btb/PortableIIMemBoard/System Memory Board.kicad_sch

## KiCad design System Memory Board.kicad_sch (2024-03-25)

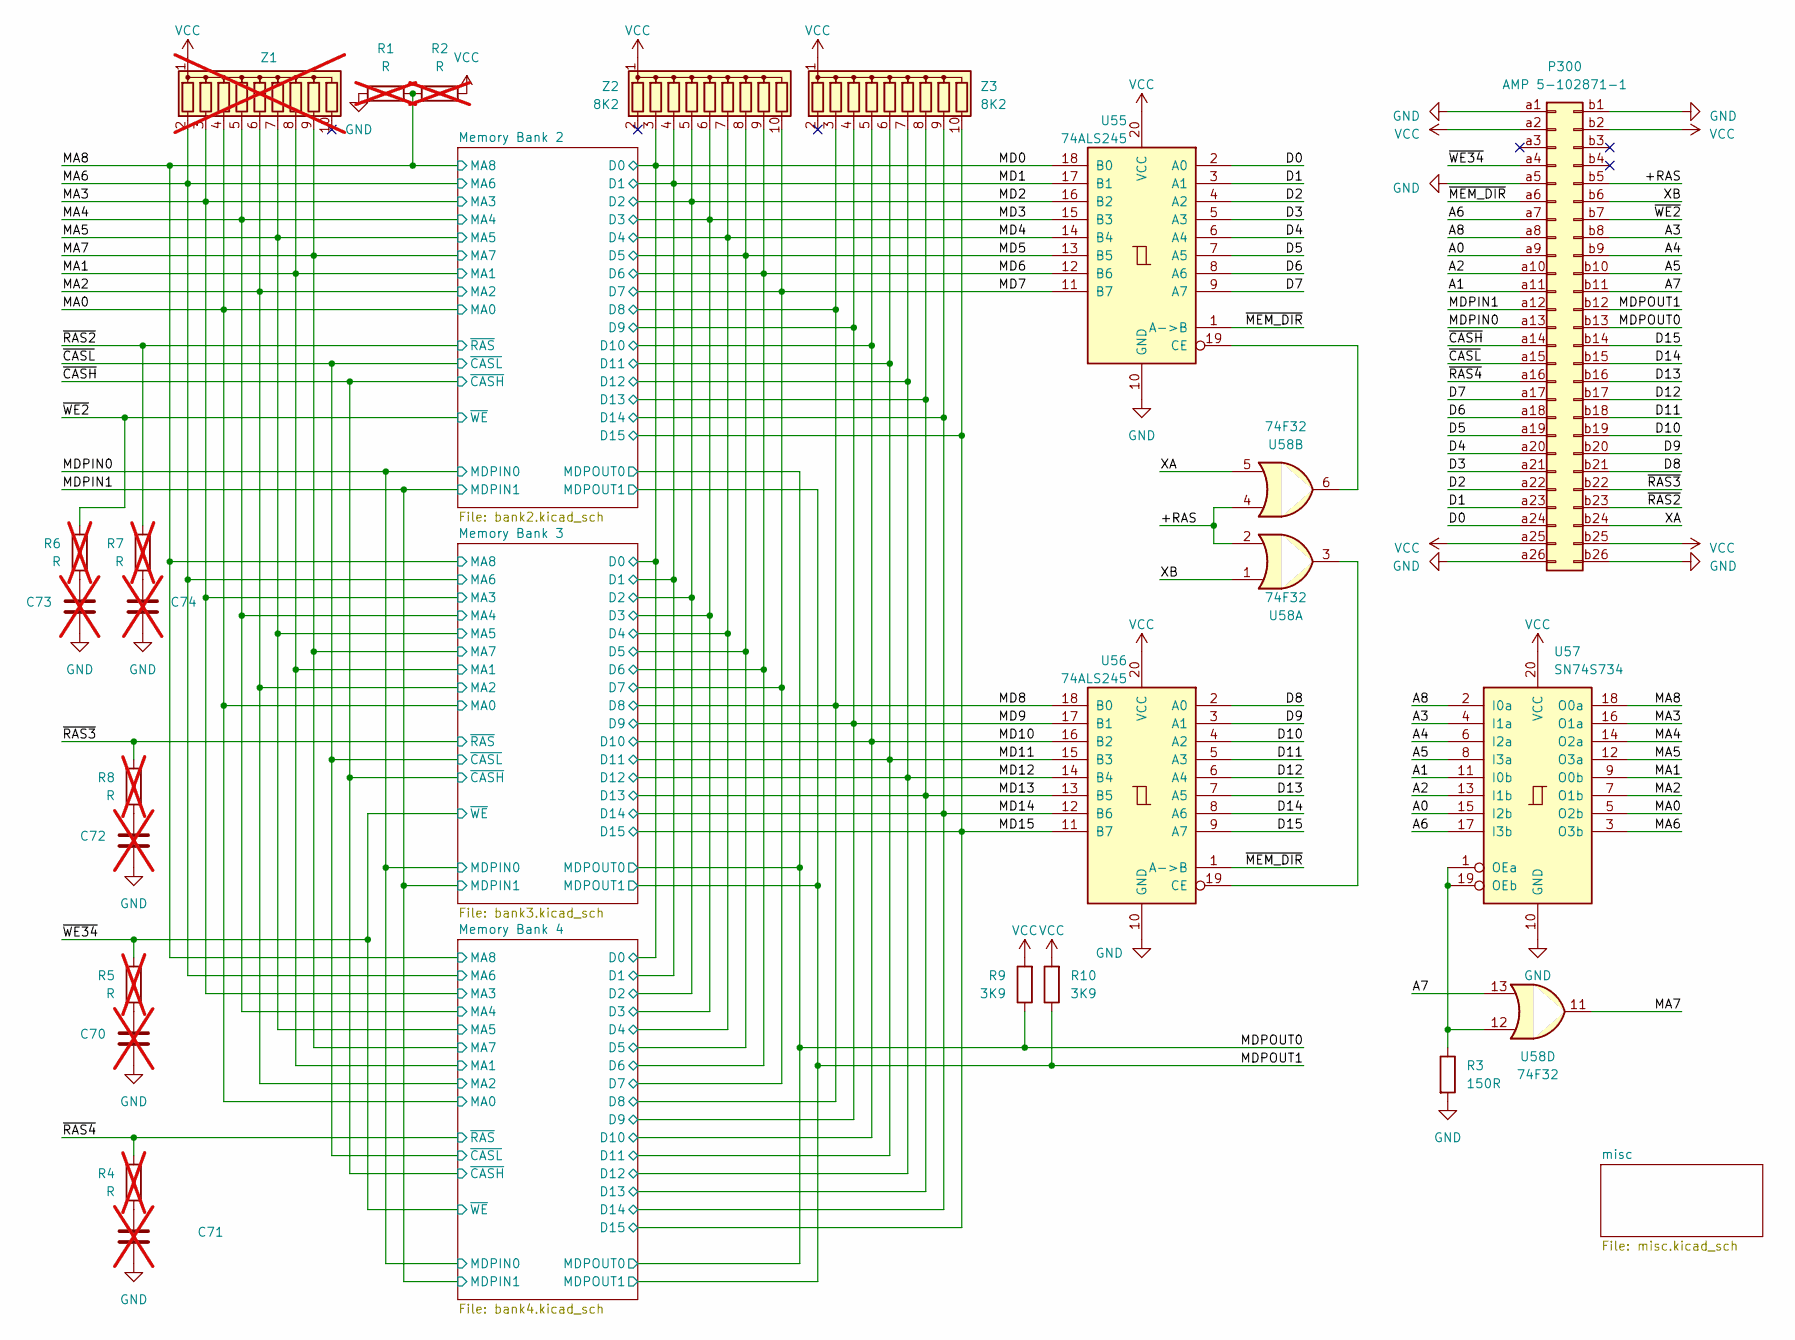
[picture p3: schematic System Memory Board.kicad_sch]

Parts:
C70, C71, C72, C73, C74: C_Rect_L7.0mm_W2.0mm_P5.00mm; not fitted
P300: AMP 5-102871-1
R1, R2, R4, R5, R6, R7, R8: R; R_Axial_DIN0309_L9.0mm_D3.2mm_P12.70mm_Horizontal; not fitted
R3: 150R; R_Axial_DIN0309_L9.0mm_D3.2mm_P12.70mm_Horizontal
R9, R10: 3K9; R_Axial_DIN0309_L9.0mm_D3.2mm_P12.70mm_Horizontal
U55, U56: 74ALS245; DIP-20_W7.62mm
U57: SN74S734; DIP-20_W7.62mm
U58: 74F32; DIP-14_W7.62mm
Z1: R_Array_SIP10; not fitted
Z2, Z3: 8K2; R_Array_SIP10

Connections:
+RAS: P300.b5, U58.2, U58.4
A0: P300.a9, U57.15 (I2b)
A1: P300.a11, U57.11 (I0b)
A2: P300.a10, U57.13 (I1b)
A3: P300.b8, U57.4 (I1a)
A4: P300.b9, U57.6 (I2a)
A5: P300.b10, U57.8 (I3a)
A6: P300.a7, U57.17 (I3b)
A7: P300.b11, U58.13
A8: P300.a8, U57.2 (I0a)
D0: P300.a24, U55.2 (A0)
D1: P300.a23, U55.3 (A1)
D2: P300.a22, U55.4 (A2)
D3: P300.a21, U55.5 (A3)
D4: P300.a20, U55.6 (A4)
D5: P300.a19, U55.7 (A5)
D6: P300.a18, U55.8 (A6)
D7: P300.a17, U55.9 (A7)
D8: P300.b21, U56.2 (A0)
D9: P300.b20, U56.3 (A1)
D10: P300.b19, U56.4 (A2)
D11: P300.b18, U56.5 (A3)
D12: P300.b17, U56.6 (A4)
D13: P300.b16, U56.7 (A5)
D14: P300.b15, U56.8 (A6)
D15: P300.b14, U56.9 (A7)
GND: C70.2, C71.2, C72.2, C73.2, C74.2, P300.a1, P300.a5, P300.a26, P300.b1, P300.b26, R1.1, R3.2, U55.10 (GND), U56.10 (GND), U57.10 (GND)
MA0: U57.5 (O2b), Z1.4 (R3)
MA1: U57.9 (O0b), Z1.8 (R7)
MA2: U57.7 (O1b), Z1.6 (R5)
MA3: U57.16 (O1a), Z1.3 (R2)
MA4: U57.14 (O2a), Z1.5 (R4)
MA5: U57.12 (O3a), Z1.7 (R6)
MA6: U57.3 (O3b), Z1.2 (R1)
MA7: U58.11, Z1.9 (R8)
MA8: R1.2, R2.2, U57.18 (O0a)
MD0: U55.18 (B0), Z2.3 (R2)
MD1: U55.17 (B1), Z2.4 (R3)
MD2: U55.16 (B2), Z2.5 (R4)
MD3: U55.15 (B3), Z2.6 (R5)
MD4: U55.14 (B4), Z2.7 (R6)
MD5: U55.13 (B5), Z2.8 (R7)
MD6: U55.12 (B6), Z2.9 (R8)
MD7: U55.11 (B7), Z2.10 (R9)
MD8: U56.18 (B0), Z3.3 (R2)
MD9: U56.17 (B1), Z3.4 (R3)
MD10: U56.16 (B2), Z3.5 (R4)
MD11: U56.15 (B3), Z3.6 (R5)
MD12: U56.14 (B4), Z3.7 (R6)
MD13: U56.13 (B5), Z3.8 (R7)
MD14: U56.12 (B6), Z3.9 (R8)
MD15: U56.11 (B7), Z3.10 (R9)
MDPIN0: P300.a13
MDPIN1: P300.a12
MDPOUT0: P300.b13, R9.1
MDPOUT1: P300.b12, R10.1
unnamed: C70.1, R5.2
unnamed: C71.1, R4.1
unnamed: C72.1, R8.1
unnamed: C73.1, R6.1
unnamed: C74.1, R7.1
unnamed: R3.1, U57.1 (OEa), U57.19 (OEb), U58.12
unnamed: U55.19 (CE), U58.6
unnamed: U56.19 (CE), U58.3
VCC: P300.a2, P300.a25, P300.b2, P300.b25, R2.1, R9.2, R10.2, U55.20 (VCC), U56.20 (VCC), U57.20 (VCC), Z1.1 (common), Z2.1 (common), Z3.1 (common)
XA: P300.b24, U58.5
XB: P300.b6, U58.1
~CASH: P300.a14
~CASL: P300.a15
~MEM_DIR: P300.a6, U55.1 (A->B), U56.1 (A->B)
~RAS2: P300.b23, R7.2
~RAS3: P300.b22, R8.2
~RAS4: P300.a16, R4.2
~WE2: P300.b7, R6.2
~WE34: P300.a4, R5.1
