btb/PortableIIMemBoard/bank2.kicad_sch

## KiCad design bank2.kicad_sch (2024-03-24)

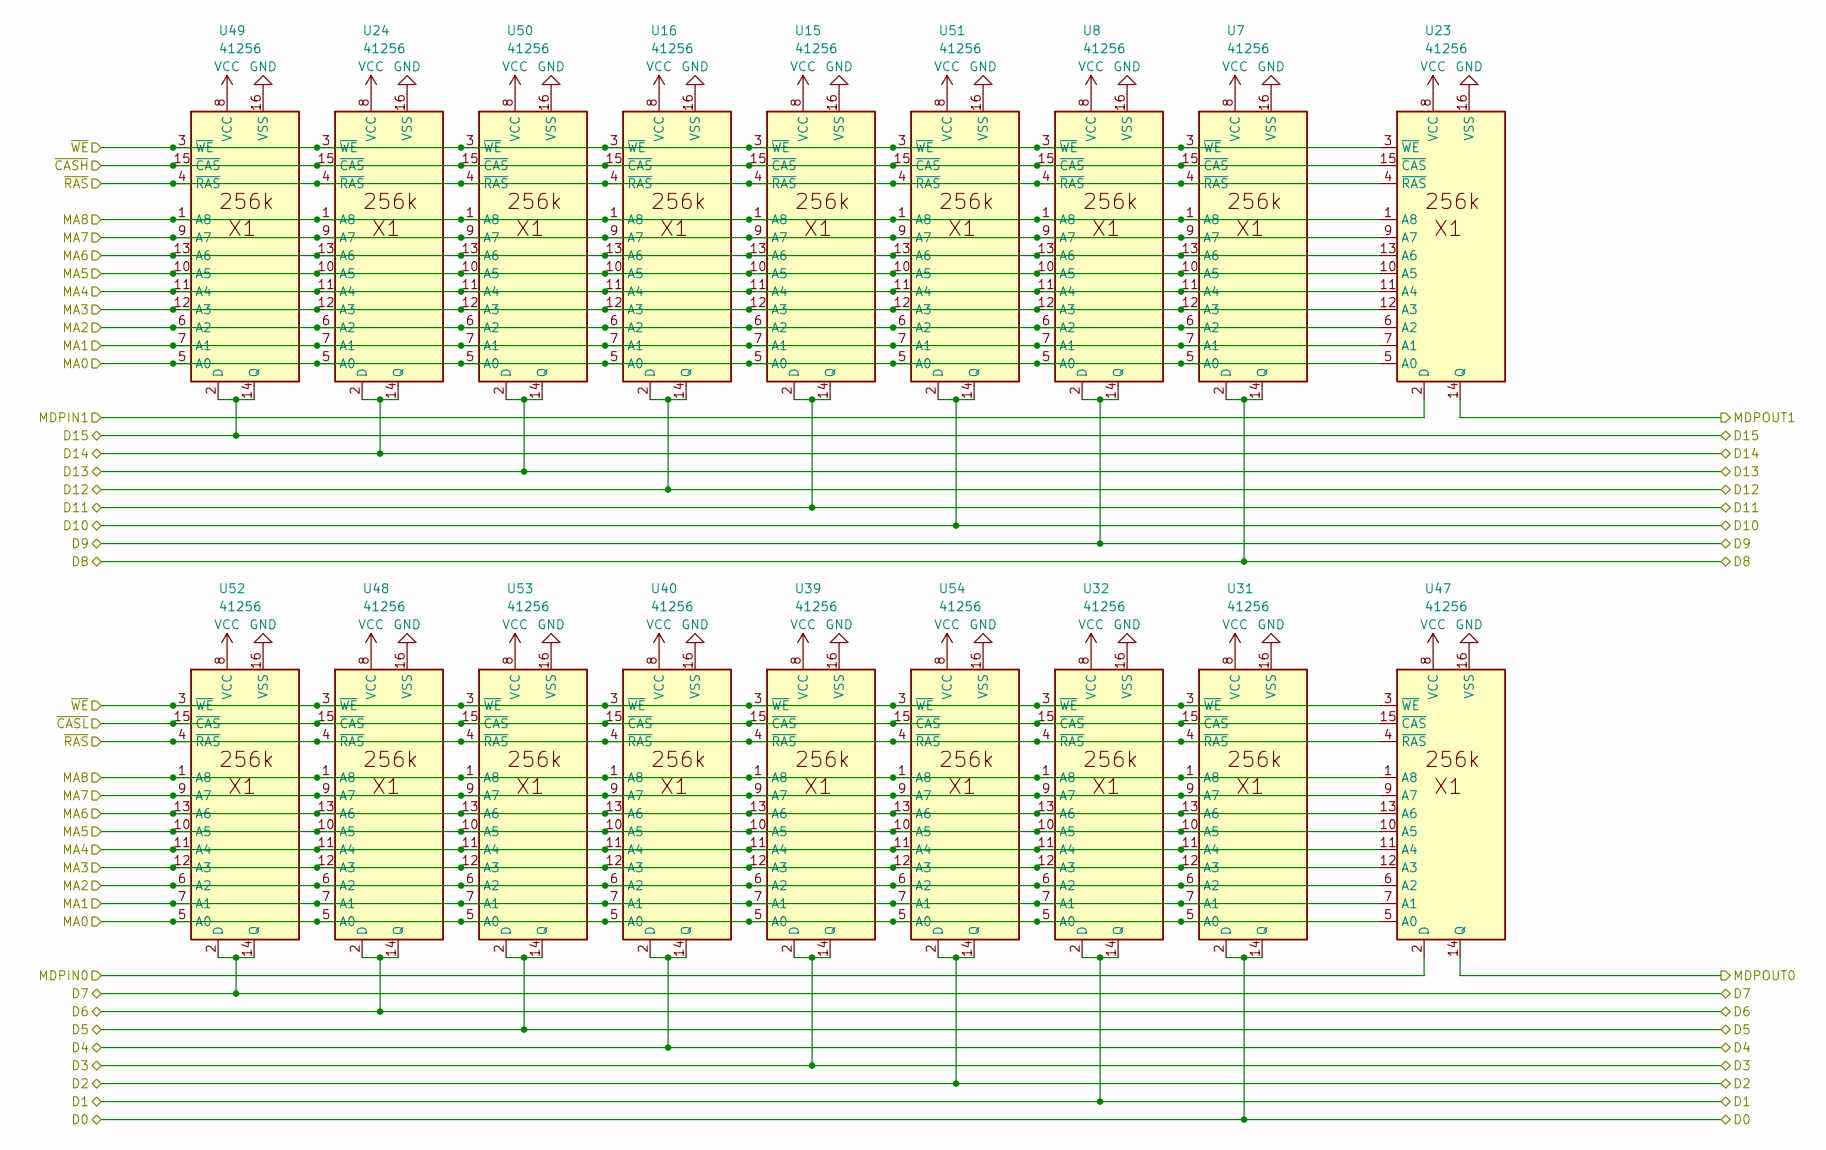
[picture p4: schematic bank2.kicad_sch]

Parts:
U7, U8, U15, U16, U23, U24, U31, U32, U39, U40, U47, U48, U49, U50, U51, U52, U53, U54: 41256; DIP-16_W7.62mm

Connections:
D0: U31.2 (D), U31.14 (Q)
D1: U32.2 (D), U32.14 (Q)
D2: U54.2 (D), U54.14 (Q)
D3: U39.2 (D), U39.14 (Q)
D4: U40.2 (D), U40.14 (Q)
D5: U53.2 (D), U53.14 (Q)
D6: U48.2 (D), U48.14 (Q)
D7: U52.2 (D), U52.14 (Q)
D8: U7.2 (D), U7.14 (Q)
D9: U8.2 (D), U8.14 (Q)
D10: U51.2 (D), U51.14 (Q)
D11: U15.2 (D), U15.14 (Q)
D12: U16.2 (D), U16.14 (Q)
D13: U50.2 (D), U50.14 (Q)
D14: U24.2 (D), U24.14 (Q)
D15: U49.2 (D), U49.14 (Q)
GND: U7.16 (VSS), U8.16 (VSS), U15.16 (VSS), U16.16 (VSS), U23.16 (VSS), U24.16 (VSS), U31.16 (VSS), U32.16 (VSS), U39.16 (VSS), U40.16 (VSS), U47.16 (VSS), U48.16 (VSS), U49.16 (VSS), U50.16 (VSS), U51.16 (VSS), U52.16 (VSS), U53.16 (VSS), U54.16 (VSS)
MA0: U7.5 (A0), U8.5 (A0), U15.5 (A0), U16.5 (A0), U23.5 (A0), U24.5 (A0), U31.5 (A0), U32.5 (A0), U39.5 (A0), U40.5 (A0), U47.5 (A0), U48.5 (A0), U49.5 (A0), U50.5 (A0), U51.5 (A0), U52.5 (A0), U53.5 (A0), U54.5 (A0)
MA1: U7.7 (A1), U8.7 (A1), U15.7 (A1), U16.7 (A1), U23.7 (A1), U24.7 (A1), U31.7 (A1), U32.7 (A1), U39.7 (A1), U40.7 (A1), U47.7 (A1), U48.7 (A1), U49.7 (A1), U50.7 (A1), U51.7 (A1), U52.7 (A1), U53.7 (A1), U54.7 (A1)
MA2: U7.6 (A2), U8.6 (A2), U15.6 (A2), U16.6 (A2), U23.6 (A2), U24.6 (A2), U31.6 (A2), U32.6 (A2), U39.6 (A2), U40.6 (A2), U47.6 (A2), U48.6 (A2), U49.6 (A2), U50.6 (A2), U51.6 (A2), U52.6 (A2), U53.6 (A2), U54.6 (A2)
MA3: U7.12 (A3), U8.12 (A3), U15.12 (A3), U16.12 (A3), U23.12 (A3), U24.12 (A3), U31.12 (A3), U32.12 (A3), U39.12 (A3), U40.12 (A3), U47.12 (A3), U48.12 (A3), U49.12 (A3), U50.12 (A3), U51.12 (A3), U52.12 (A3), U53.12 (A3), U54.12 (A3)
MA4: U7.11 (A4), U8.11 (A4), U15.11 (A4), U16.11 (A4), U23.11 (A4), U24.11 (A4), U31.11 (A4), U32.11 (A4), U39.11 (A4), U40.11 (A4), U47.11 (A4), U48.11 (A4), U49.11 (A4), U50.11 (A4), U51.11 (A4), U52.11 (A4), U53.11 (A4), U54.11 (A4)
MA5: U7.10 (A5), U8.10 (A5), U15.10 (A5), U16.10 (A5), U23.10 (A5), U24.10 (A5), U31.10 (A5), U32.10 (A5), U39.10 (A5), U40.10 (A5), U47.10 (A5), U48.10 (A5), U49.10 (A5), U50.10 (A5), U51.10 (A5), U52.10 (A5), U53.10 (A5), U54.10 (A5)
MA6: U7.13 (A6), U8.13 (A6), U15.13 (A6), U16.13 (A6), U23.13 (A6), U24.13 (A6), U31.13 (A6), U32.13 (A6), U39.13 (A6), U40.13 (A6), U47.13 (A6), U48.13 (A6), U49.13 (A6), U50.13 (A6), U51.13 (A6), U52.13 (A6), U53.13 (A6), U54.13 (A6)
MA7: U7.9 (A7), U8.9 (A7), U15.9 (A7), U16.9 (A7), U23.9 (A7), U24.9 (A7), U31.9 (A7), U32.9 (A7), U39.9 (A7), U40.9 (A7), U47.9 (A7), U48.9 (A7), U49.9 (A7), U50.9 (A7), U51.9 (A7), U52.9 (A7), U53.9 (A7), U54.9 (A7)
MA8: U7.1 (A8), U8.1 (A8), U15.1 (A8), U16.1 (A8), U23.1 (A8), U24.1 (A8), U31.1 (A8), U32.1 (A8), U39.1 (A8), U40.1 (A8), U47.1 (A8), U48.1 (A8), U49.1 (A8), U50.1 (A8), U51.1 (A8), U52.1 (A8), U53.1 (A8), U54.1 (A8)
MDPIN0: U47.2 (D)
MDPIN1: U23.2 (D)
MDPOUT0: U47.14 (Q)
MDPOUT1: U23.14 (Q)
VCC: U7.8 (VCC), U8.8 (VCC), U15.8 (VCC), U16.8 (VCC), U23.8 (VCC), U24.8 (VCC), U31.8 (VCC), U32.8 (VCC), U39.8 (VCC), U40.8 (VCC), U47.8 (VCC), U48.8 (VCC), U49.8 (VCC), U50.8 (VCC), U51.8 (VCC), U52.8 (VCC), U53.8 (VCC), U54.8 (VCC)
~CASH: U7.15 (~CAS), U8.15 (~CAS), U15.15 (~CAS), U16.15 (~CAS), U23.15 (~CAS), U24.15 (~CAS), U49.15 (~CAS), U50.15 (~CAS), U51.15 (~CAS)
~CASL: U31.15 (~CAS), U32.15 (~CAS), U39.15 (~CAS), U40.15 (~CAS), U47.15 (~CAS), U48.15 (~CAS), U52.15 (~CAS), U53.15 (~CAS), U54.15 (~CAS)
~RAS: U7.4 (~RAS), U8.4 (~RAS), U15.4 (~RAS), U16.4 (~RAS), U23.4 (~RAS), U24.4 (~RAS), U31.4 (~RAS), U32.4 (~RAS), U39.4 (~RAS), U40.4 (~RAS), U47.4 (~RAS), U48.4 (~RAS), U49.4 (~RAS), U50.4 (~RAS), U51.4 (~RAS), U52.4 (~RAS), U53.4 (~RAS), U54.4 (~RAS)
~WE: U7.3 (~WE), U8.3 (~WE), U15.3 (~WE), U16.3 (~WE), U23.3 (~WE), U24.3 (~WE), U31.3 (~WE), U32.3 (~WE), U39.3 (~WE), U40.3 (~WE), U47.3 (~WE), U48.3 (~WE), U49.3 (~WE), U50.3 (~WE), U51.3 (~WE), U52.3 (~WE), U53.3 (~WE), U54.3 (~WE)
