btb/PortableIIMemBoard/bank3.kicad_sch

## KiCad design bank3.kicad_sch (2024-03-25)

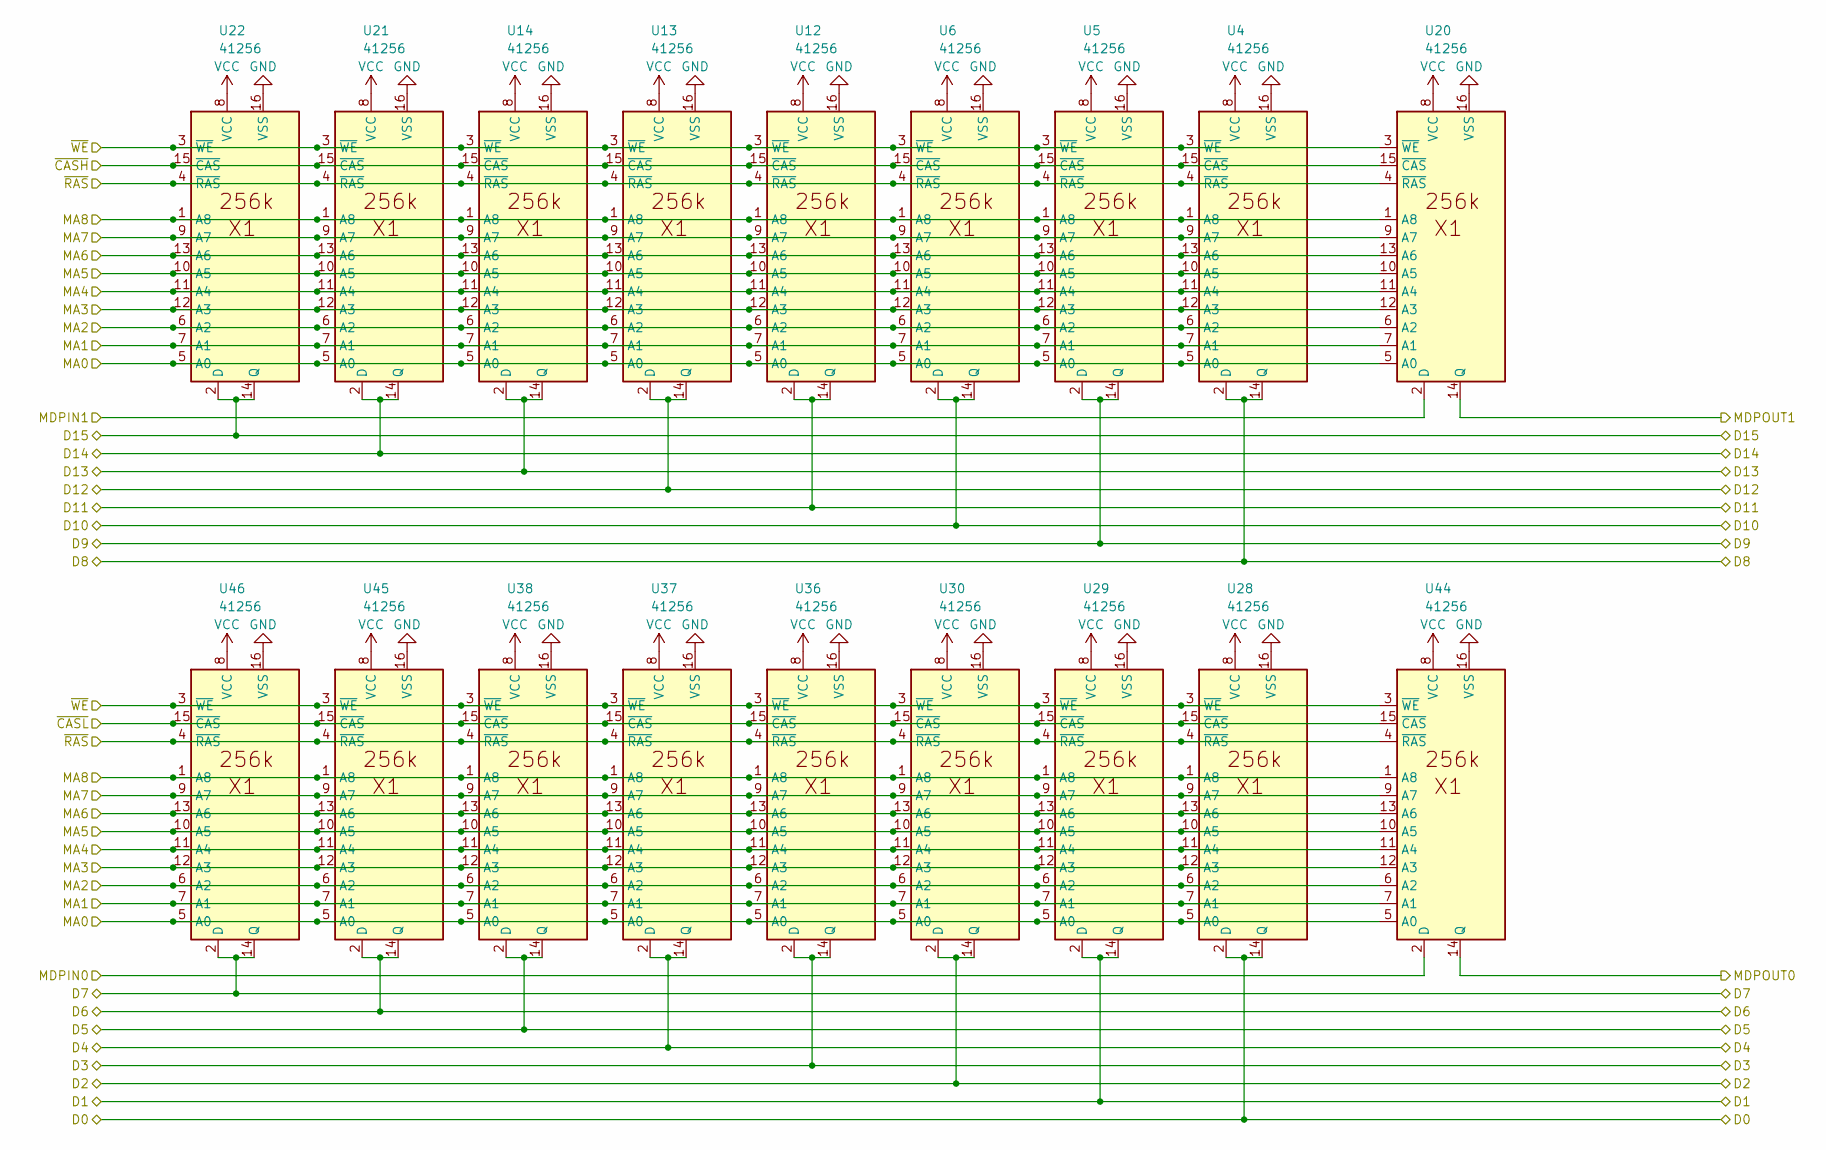
[picture p5: schematic bank3.kicad_sch]

Parts:
U4, U5, U6, U12, U13, U14, U20, U21, U22, U28, U29, U30, U36, U37, U38, U44, U45, U46: 41256; DIP-16_W7.62mm_Socket

Connections:
D0: U28.2 (D), U28.14 (Q)
D1: U29.2 (D), U29.14 (Q)
D2: U30.2 (D), U30.14 (Q)
D3: U36.2 (D), U36.14 (Q)
D4: U37.2 (D), U37.14 (Q)
D5: U38.2 (D), U38.14 (Q)
D6: U45.2 (D), U45.14 (Q)
D7: U46.2 (D), U46.14 (Q)
D8: U4.2 (D), U4.14 (Q)
D9: U5.2 (D), U5.14 (Q)
D10: U6.2 (D), U6.14 (Q)
D11: U12.2 (D), U12.14 (Q)
D12: U13.2 (D), U13.14 (Q)
D13: U14.2 (D), U14.14 (Q)
D14: U21.2 (D), U21.14 (Q)
D15: U22.2 (D), U22.14 (Q)
GND: U4.16 (VSS), U5.16 (VSS), U6.16 (VSS), U12.16 (VSS), U13.16 (VSS), U14.16 (VSS), U20.16 (VSS), U21.16 (VSS), U22.16 (VSS), U28.16 (VSS), U29.16 (VSS), U30.16 (VSS), U36.16 (VSS), U37.16 (VSS), U38.16 (VSS), U44.16 (VSS), U45.16 (VSS), U46.16 (VSS)
MA0: U4.5 (A0), U5.5 (A0), U6.5 (A0), U12.5 (A0), U13.5 (A0), U14.5 (A0), U20.5 (A0), U21.5 (A0), U22.5 (A0), U28.5 (A0), U29.5 (A0), U30.5 (A0), U36.5 (A0), U37.5 (A0), U38.5 (A0), U44.5 (A0), U45.5 (A0), U46.5 (A0)
MA1: U4.7 (A1), U5.7 (A1), U6.7 (A1), U12.7 (A1), U13.7 (A1), U14.7 (A1), U20.7 (A1), U21.7 (A1), U22.7 (A1), U28.7 (A1), U29.7 (A1), U30.7 (A1), U36.7 (A1), U37.7 (A1), U38.7 (A1), U44.7 (A1), U45.7 (A1), U46.7 (A1)
MA2: U4.6 (A2), U5.6 (A2), U6.6 (A2), U12.6 (A2), U13.6 (A2), U14.6 (A2), U20.6 (A2), U21.6 (A2), U22.6 (A2), U28.6 (A2), U29.6 (A2), U30.6 (A2), U36.6 (A2), U37.6 (A2), U38.6 (A2), U44.6 (A2), U45.6 (A2), U46.6 (A2)
MA3: U4.12 (A3), U5.12 (A3), U6.12 (A3), U12.12 (A3), U13.12 (A3), U14.12 (A3), U20.12 (A3), U21.12 (A3), U22.12 (A3), U28.12 (A3), U29.12 (A3), U30.12 (A3), U36.12 (A3), U37.12 (A3), U38.12 (A3), U44.12 (A3), U45.12 (A3), U46.12 (A3)
MA4: U4.11 (A4), U5.11 (A4), U6.11 (A4), U12.11 (A4), U13.11 (A4), U14.11 (A4), U20.11 (A4), U21.11 (A4), U22.11 (A4), U28.11 (A4), U29.11 (A4), U30.11 (A4), U36.11 (A4), U37.11 (A4), U38.11 (A4), U44.11 (A4), U45.11 (A4), U46.11 (A4)
MA5: U4.10 (A5), U5.10 (A5), U6.10 (A5), U12.10 (A5), U13.10 (A5), U14.10 (A5), U20.10 (A5), U21.10 (A5), U22.10 (A5), U28.10 (A5), U29.10 (A5), U30.10 (A5), U36.10 (A5), U37.10 (A5), U38.10 (A5), U44.10 (A5), U45.10 (A5), U46.10 (A5)
MA6: U4.13 (A6), U5.13 (A6), U6.13 (A6), U12.13 (A6), U13.13 (A6), U14.13 (A6), U20.13 (A6), U21.13 (A6), U22.13 (A6), U28.13 (A6), U29.13 (A6), U30.13 (A6), U36.13 (A6), U37.13 (A6), U38.13 (A6), U44.13 (A6), U45.13 (A6), U46.13 (A6)
MA7: U4.9 (A7), U5.9 (A7), U6.9 (A7), U12.9 (A7), U13.9 (A7), U14.9 (A7), U20.9 (A7), U21.9 (A7), U22.9 (A7), U28.9 (A7), U29.9 (A7), U30.9 (A7), U36.9 (A7), U37.9 (A7), U38.9 (A7), U44.9 (A7), U45.9 (A7), U46.9 (A7)
MA8: U4.1 (A8), U5.1 (A8), U6.1 (A8), U12.1 (A8), U13.1 (A8), U14.1 (A8), U20.1 (A8), U21.1 (A8), U22.1 (A8), U28.1 (A8), U29.1 (A8), U30.1 (A8), U36.1 (A8), U37.1 (A8), U38.1 (A8), U44.1 (A8), U45.1 (A8), U46.1 (A8)
MDPIN0: U44.2 (D)
MDPIN1: U20.2 (D)
MDPOUT0: U44.14 (Q)
MDPOUT1: U20.14 (Q)
VCC: U4.8 (VCC), U5.8 (VCC), U6.8 (VCC), U12.8 (VCC), U13.8 (VCC), U14.8 (VCC), U20.8 (VCC), U21.8 (VCC), U22.8 (VCC), U28.8 (VCC), U29.8 (VCC), U30.8 (VCC), U36.8 (VCC), U37.8 (VCC), U38.8 (VCC), U44.8 (VCC), U45.8 (VCC), U46.8 (VCC)
~CASH: U4.15 (~CAS), U5.15 (~CAS), U6.15 (~CAS), U12.15 (~CAS), U13.15 (~CAS), U14.15 (~CAS), U20.15 (~CAS), U21.15 (~CAS), U22.15 (~CAS)
~CASL: U28.15 (~CAS), U29.15 (~CAS), U30.15 (~CAS), U36.15 (~CAS), U37.15 (~CAS), U38.15 (~CAS), U44.15 (~CAS), U45.15 (~CAS), U46.15 (~CAS)
~RAS: U4.4 (~RAS), U5.4 (~RAS), U6.4 (~RAS), U12.4 (~RAS), U13.4 (~RAS), U14.4 (~RAS), U20.4 (~RAS), U21.4 (~RAS), U22.4 (~RAS), U28.4 (~RAS), U29.4 (~RAS), U30.4 (~RAS), U36.4 (~RAS), U37.4 (~RAS), U38.4 (~RAS), U44.4 (~RAS), U45.4 (~RAS), U46.4 (~RAS)
~WE: U4.3 (~WE), U5.3 (~WE), U6.3 (~WE), U12.3 (~WE), U13.3 (~WE), U14.3 (~WE), U20.3 (~WE), U21.3 (~WE), U22.3 (~WE), U28.3 (~WE), U29.3 (~WE), U30.3 (~WE), U36.3 (~WE), U37.3 (~WE), U38.3 (~WE), U44.3 (~WE), U45.3 (~WE), U46.3 (~WE)
