btb/PortableIIMemBoard/bank4.kicad_sch

## KiCad design bank4.kicad_sch (2024-03-24)

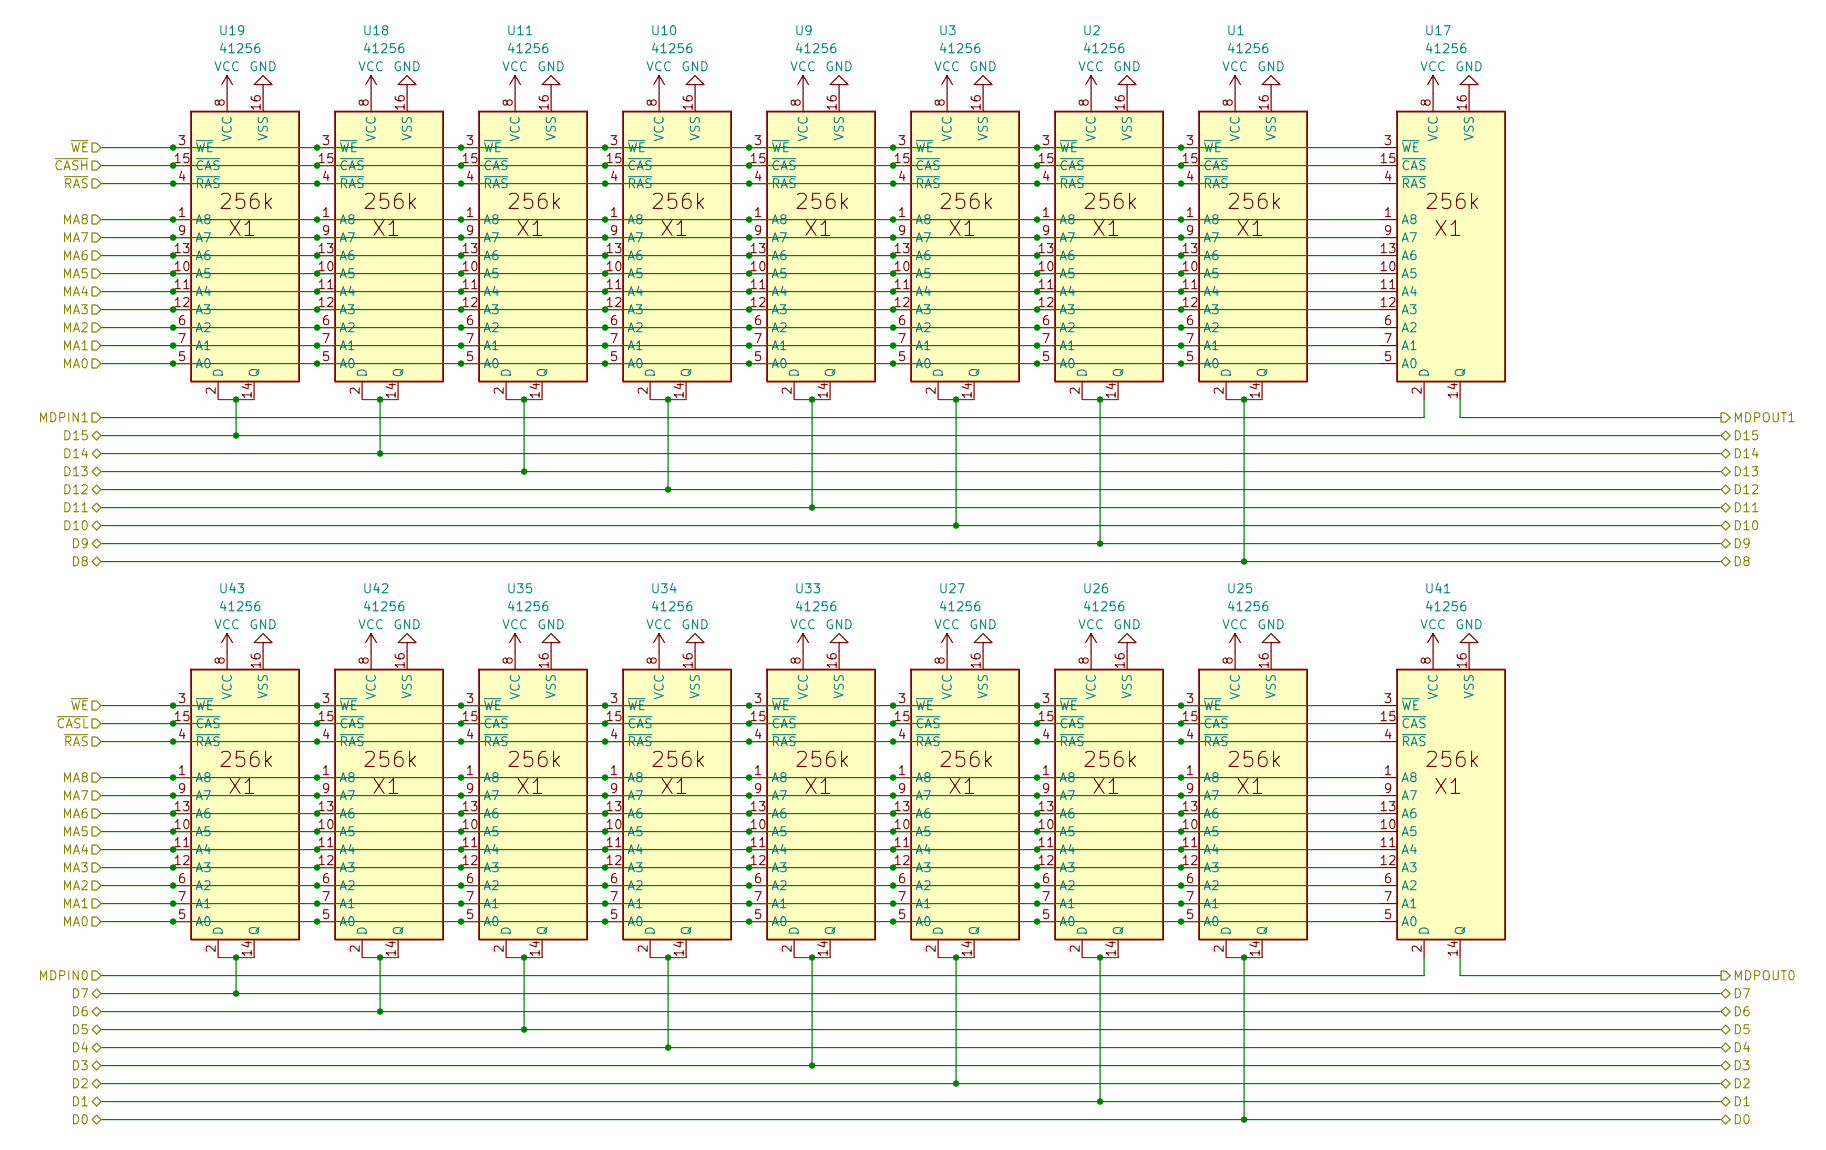
[picture p6: schematic bank4.kicad_sch]

Parts:
U1, U2, U3, U9, U10, U11, U17, U18, U19, U25, U26, U27, U33, U34, U35, U41, U42, U43: 41256; DIP-16_W7.62mm_Socket

Connections:
D0: U25.2 (D), U25.14 (Q)
D1: U26.2 (D), U26.14 (Q)
D2: U27.2 (D), U27.14 (Q)
D3: U33.2 (D), U33.14 (Q)
D4: U34.2 (D), U34.14 (Q)
D5: U35.2 (D), U35.14 (Q)
D6: U42.2 (D), U42.14 (Q)
D7: U43.2 (D), U43.14 (Q)
D8: U1.2 (D), U1.14 (Q)
D9: U2.2 (D), U2.14 (Q)
D10: U3.2 (D), U3.14 (Q)
D11: U9.2 (D), U9.14 (Q)
D12: U10.2 (D), U10.14 (Q)
D13: U11.2 (D), U11.14 (Q)
D14: U18.2 (D), U18.14 (Q)
D15: U19.2 (D), U19.14 (Q)
GND: U1.16 (VSS), U2.16 (VSS), U3.16 (VSS), U9.16 (VSS), U10.16 (VSS), U11.16 (VSS), U17.16 (VSS), U18.16 (VSS), U19.16 (VSS), U25.16 (VSS), U26.16 (VSS), U27.16 (VSS), U33.16 (VSS), U34.16 (VSS), U35.16 (VSS), U41.16 (VSS), U42.16 (VSS), U43.16 (VSS)
MA0: U1.5 (A0), U2.5 (A0), U3.5 (A0), U9.5 (A0), U10.5 (A0), U11.5 (A0), U17.5 (A0), U18.5 (A0), U19.5 (A0), U25.5 (A0), U26.5 (A0), U27.5 (A0), U33.5 (A0), U34.5 (A0), U35.5 (A0), U41.5 (A0), U42.5 (A0), U43.5 (A0)
MA1: U1.7 (A1), U2.7 (A1), U3.7 (A1), U9.7 (A1), U10.7 (A1), U11.7 (A1), U17.7 (A1), U18.7 (A1), U19.7 (A1), U25.7 (A1), U26.7 (A1), U27.7 (A1), U33.7 (A1), U34.7 (A1), U35.7 (A1), U41.7 (A1), U42.7 (A1), U43.7 (A1)
MA2: U1.6 (A2), U2.6 (A2), U3.6 (A2), U9.6 (A2), U10.6 (A2), U11.6 (A2), U17.6 (A2), U18.6 (A2), U19.6 (A2), U25.6 (A2), U26.6 (A2), U27.6 (A2), U33.6 (A2), U34.6 (A2), U35.6 (A2), U41.6 (A2), U42.6 (A2), U43.6 (A2)
MA3: U1.12 (A3), U2.12 (A3), U3.12 (A3), U9.12 (A3), U10.12 (A3), U11.12 (A3), U17.12 (A3), U18.12 (A3), U19.12 (A3), U25.12 (A3), U26.12 (A3), U27.12 (A3), U33.12 (A3), U34.12 (A3), U35.12 (A3), U41.12 (A3), U42.12 (A3), U43.12 (A3)
MA4: U1.11 (A4), U2.11 (A4), U3.11 (A4), U9.11 (A4), U10.11 (A4), U11.11 (A4), U17.11 (A4), U18.11 (A4), U19.11 (A4), U25.11 (A4), U26.11 (A4), U27.11 (A4), U33.11 (A4), U34.11 (A4), U35.11 (A4), U41.11 (A4), U42.11 (A4), U43.11 (A4)
MA5: U1.10 (A5), U2.10 (A5), U3.10 (A5), U9.10 (A5), U10.10 (A5), U11.10 (A5), U17.10 (A5), U18.10 (A5), U19.10 (A5), U25.10 (A5), U26.10 (A5), U27.10 (A5), U33.10 (A5), U34.10 (A5), U35.10 (A5), U41.10 (A5), U42.10 (A5), U43.10 (A5)
MA6: U1.13 (A6), U2.13 (A6), U3.13 (A6), U9.13 (A6), U10.13 (A6), U11.13 (A6), U17.13 (A6), U18.13 (A6), U19.13 (A6), U25.13 (A6), U26.13 (A6), U27.13 (A6), U33.13 (A6), U34.13 (A6), U35.13 (A6), U41.13 (A6), U42.13 (A6), U43.13 (A6)
MA7: U1.9 (A7), U2.9 (A7), U3.9 (A7), U9.9 (A7), U10.9 (A7), U11.9 (A7), U17.9 (A7), U18.9 (A7), U19.9 (A7), U25.9 (A7), U26.9 (A7), U27.9 (A7), U33.9 (A7), U34.9 (A7), U35.9 (A7), U41.9 (A7), U42.9 (A7), U43.9 (A7)
MA8: U1.1 (A8), U2.1 (A8), U3.1 (A8), U9.1 (A8), U10.1 (A8), U11.1 (A8), U17.1 (A8), U18.1 (A8), U19.1 (A8), U25.1 (A8), U26.1 (A8), U27.1 (A8), U33.1 (A8), U34.1 (A8), U35.1 (A8), U41.1 (A8), U42.1 (A8), U43.1 (A8)
MDPIN0: U41.2 (D)
MDPIN1: U17.2 (D)
MDPOUT0: U41.14 (Q)
MDPOUT1: U17.14 (Q)
VCC: U1.8 (VCC), U2.8 (VCC), U3.8 (VCC), U9.8 (VCC), U10.8 (VCC), U11.8 (VCC), U17.8 (VCC), U18.8 (VCC), U19.8 (VCC), U25.8 (VCC), U26.8 (VCC), U27.8 (VCC), U33.8 (VCC), U34.8 (VCC), U35.8 (VCC), U41.8 (VCC), U42.8 (VCC), U43.8 (VCC)
~CASH: U1.15 (~CAS), U2.15 (~CAS), U3.15 (~CAS), U9.15 (~CAS), U10.15 (~CAS), U11.15 (~CAS), U17.15 (~CAS), U18.15 (~CAS), U19.15 (~CAS)
~CASL: U25.15 (~CAS), U26.15 (~CAS), U27.15 (~CAS), U33.15 (~CAS), U34.15 (~CAS), U35.15 (~CAS), U41.15 (~CAS), U42.15 (~CAS), U43.15 (~CAS)
~RAS: U1.4 (~RAS), U2.4 (~RAS), U3.4 (~RAS), U9.4 (~RAS), U10.4 (~RAS), U11.4 (~RAS), U17.4 (~RAS), U18.4 (~RAS), U19.4 (~RAS), U25.4 (~RAS), U26.4 (~RAS), U27.4 (~RAS), U33.4 (~RAS), U34.4 (~RAS), U35.4 (~RAS), U41.4 (~RAS), U42.4 (~RAS), U43.4 (~RAS)
~WE: U1.3 (~WE), U2.3 (~WE), U3.3 (~WE), U9.3 (~WE), U10.3 (~WE), U11.3 (~WE), U17.3 (~WE), U18.3 (~WE), U19.3 (~WE), U25.3 (~WE), U26.3 (~WE), U27.3 (~WE), U33.3 (~WE), U34.3 (~WE), U35.3 (~WE), U41.3 (~WE), U42.3 (~WE), U43.3 (~WE)
